OrionAerospace/SmashBoy/Estrutura e Acionamentos/Roda de reação/massa/dados roda de reaçao.pdf

Propriedades de massa de roda de reação
Configuração: Valor predeterminado
Sistema de coordenadas: -- valor predeterminado --

O centro da massa e os momentos de inércia são saídas no sistema de coordenadas de Montagem1 Densidade = 0.01 gramas por milímetro cúbico

Massa = 124.40 gramas

Volume = 15948.34 milímetros cúbicos

Área de superfície = 6283.67 milímetros quadrados

Centro de massa: ( milímetros )
X = -7.49
Y = -3.30
Z = 35.00

Eixos principais de inércia e momentos de inércia principais: ( gramas * milímetros quadrados ) Tomado no centro da massa.
Ix = ( 0.00, 0.00, 1.00) | Px = 23382.29
Iy = ( 1.00, 0.00, 0.00) | Py = 23382.29
Iz = ( 0.00, 1.00, 0.00) | Pz = 42605.02

Momentos de inércia: ( gramas * milímetros quadrados )
Obtido no centro de massa e alinhado com o sistema de coordenadas de saída.
Lxx = 23382.29 | Lxy = 0.00Lxz = 0.00
Lyx = 0.00 Lyy = 42605.02 | Lyz = 0.00
Lzx = 0.00Lzy = 0.00Lzz = 23382.29

Momentos de inércia: ( gramas * milímetros quadrados ) Tomados no sistema de coordenadas de saída.
Ixx = 177121.63 | Ixy = 3074.03 | Ixz = -32624.22
Iyx = 3074.03 | Iyy = 201975.89 | Iyz = -14358.64
Izx = -32624.22 | Izy = -14358.64 | Izz = 31719.72
