OrionAerospace/SmashBoy/ADCS/Orion_Sun_Sensor/SMASHBOY_AVI_ADC_PCB_PART02_V01.png

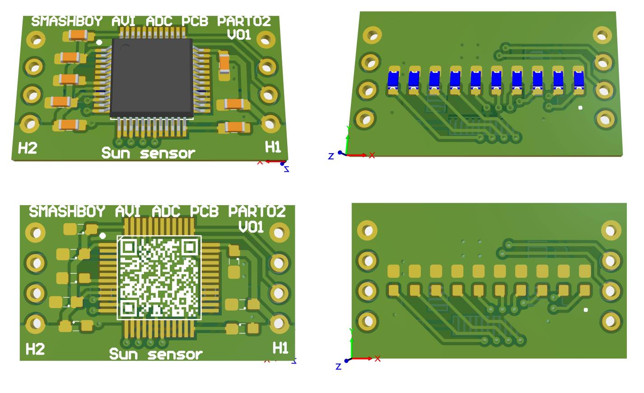
ADCS/Orion_Sun_Sensor/SMASHBOY_AVI_ADC_PCB_PART02_V01.png
