OrionAerospace/SmashBoy/Telemetria/Software/STM32/fluxograma RTOS V3.png

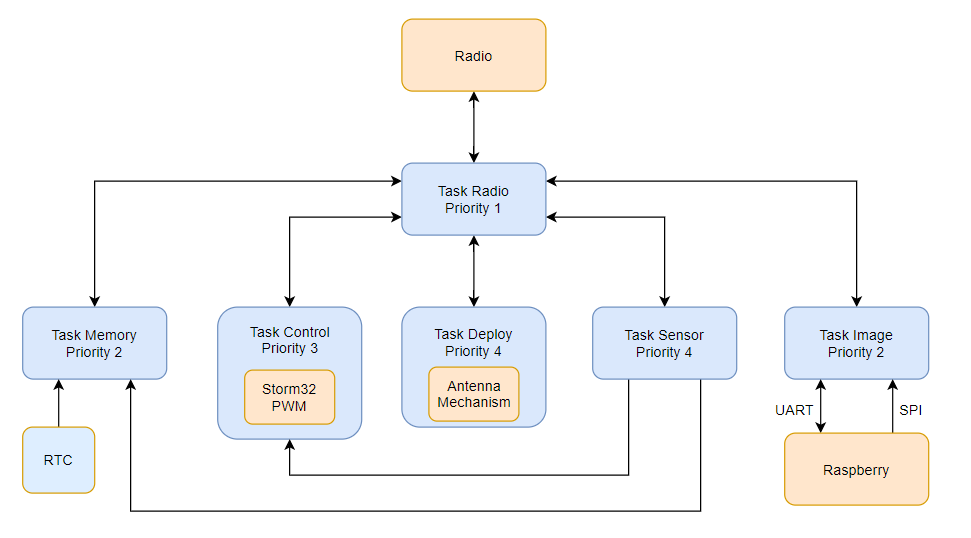
Telemetria/Software/STM32/fluxograma RTOS V3.png
