OrionAerospace/SmashBoy/Estrutura e Acionamentos/Roda de reação/massa/roda de reação.STEP

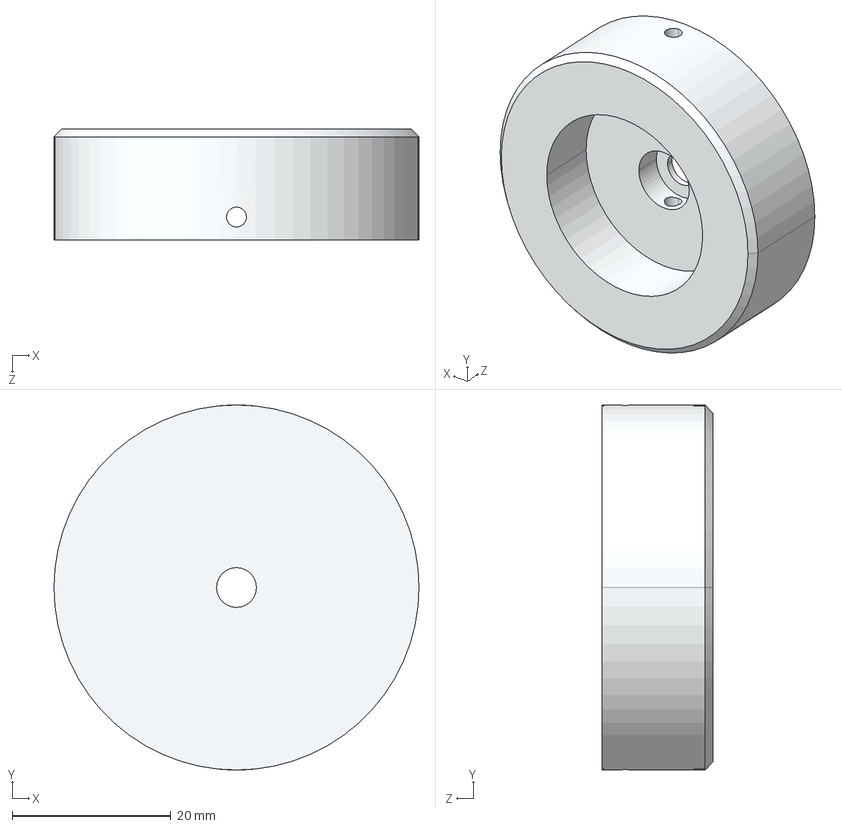
[picture p25: CAD file, 2021-03-11]
Estrutura e Acionamentos/Roda de reação/massa/roda de reação.STEP
46.0 x 46.0 x 14.0 mm
