OrionAerospace/SmashBoy/Estrutura e Acionamentos/Roda de reação/suporte.SLDPRT

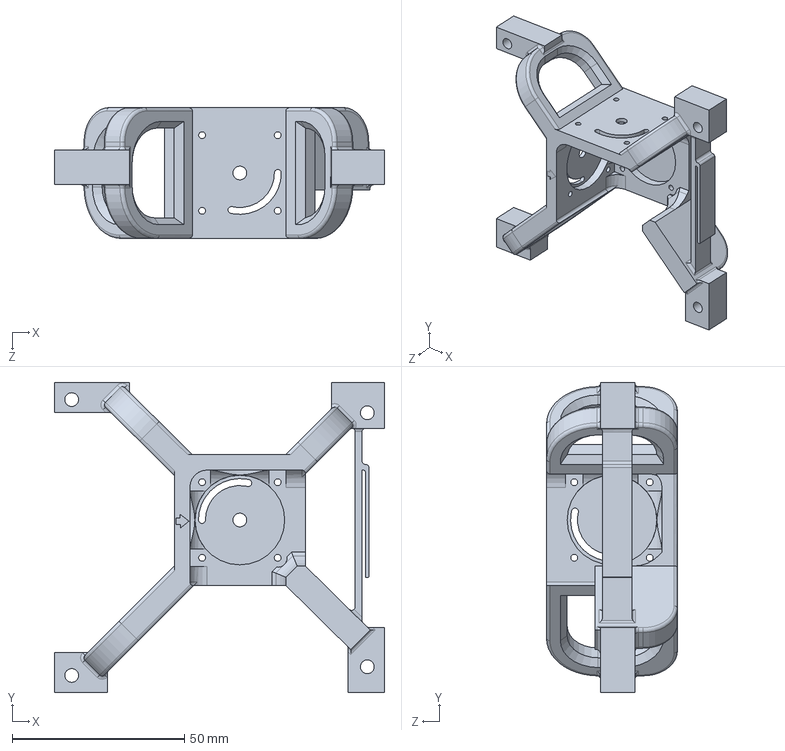
[picture p26: CAD file, 2021-02-28]
Estrutura e Acionamentos/Roda de reação/suporte.SLDPRT
95.7 x 90.0 x 38.0 mm
