OrionAerospace/SmashBoy/Estrutura e Acionamentos/trilhos/trilho-deploy-switch.SLDPRT

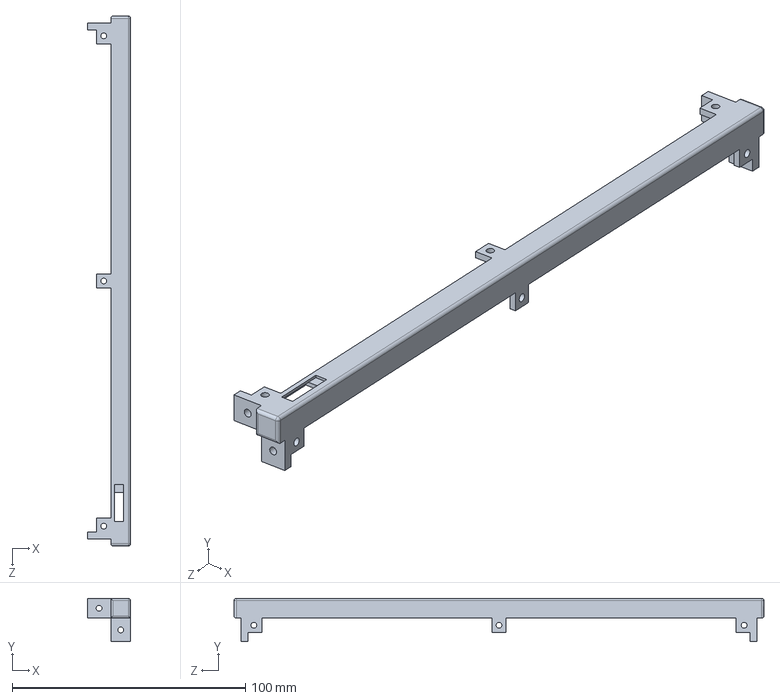
[picture p27: CAD file, 2020-08-22]
Estrutura e Acionamentos/trilhos/trilho-deploy-switch.SLDPRT
18.5 x 18.5 x 227.0 mm
