OrionAerospace/SmashBoy/ADCS/SETUP_ADCS/antigo/L3.SLDPRT

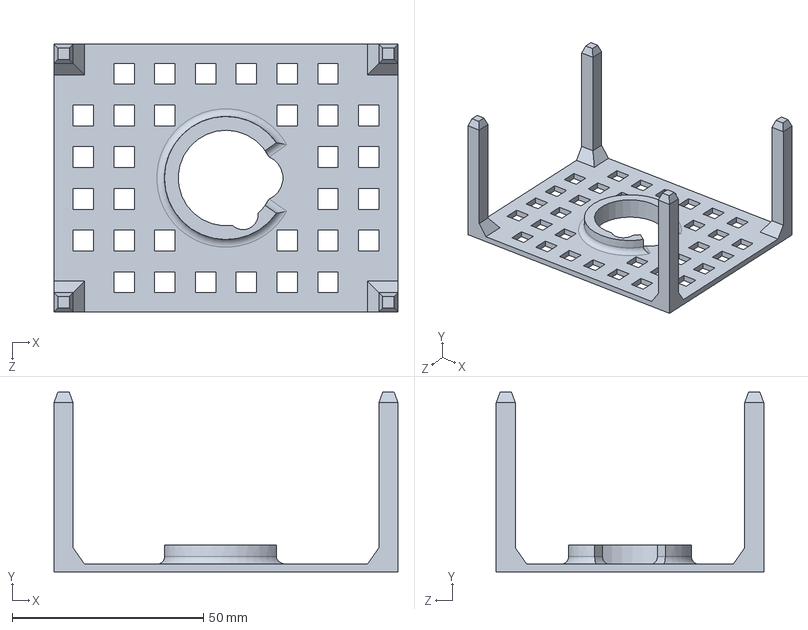
[picture p28: CAD file, 2021-07-17]
ADCS/SETUP_ADCS/antigo/L3.SLDPRT
90.0 x 47.0 x 70.0 mm
