OrionAerospace/SmashBoy/ADCS/SETUP_ADCS/STL/suporte_M.STL

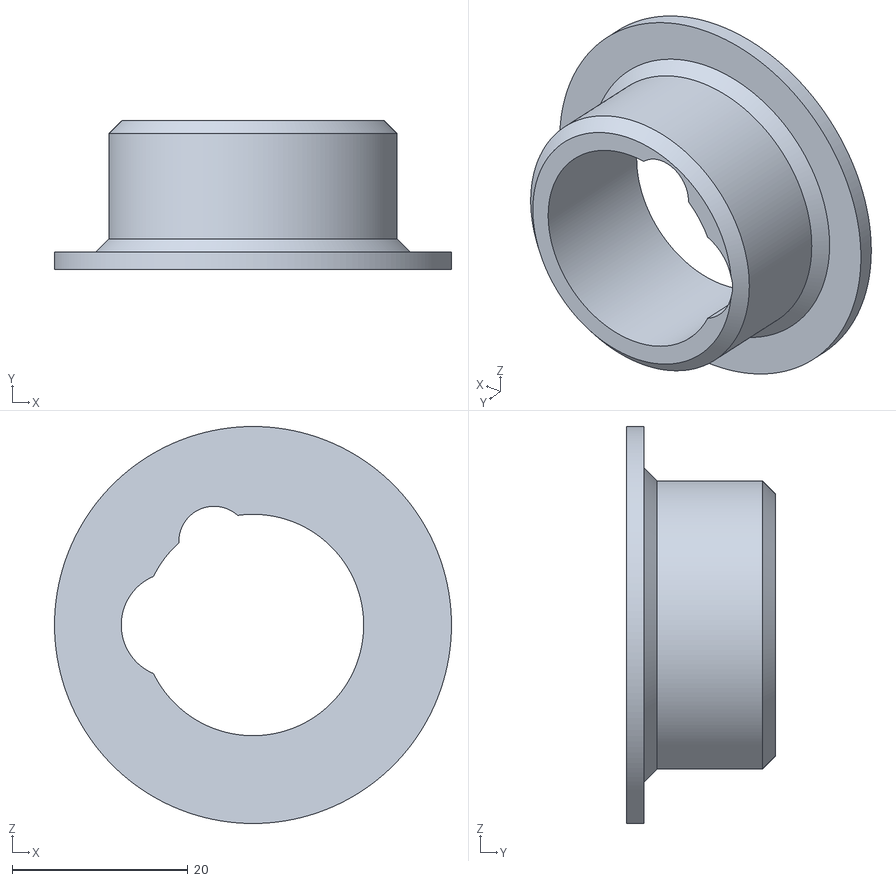
[picture p29: CAD file, 2021-07-17]
ADCS/SETUP_ADCS/STL/suporte_M.STL
45.2 x 17.0 x 45.2
