OrionAerospace/SmashBoy/ADCS/SETUP_ADCS/antigo/L2_A.SLDPRT

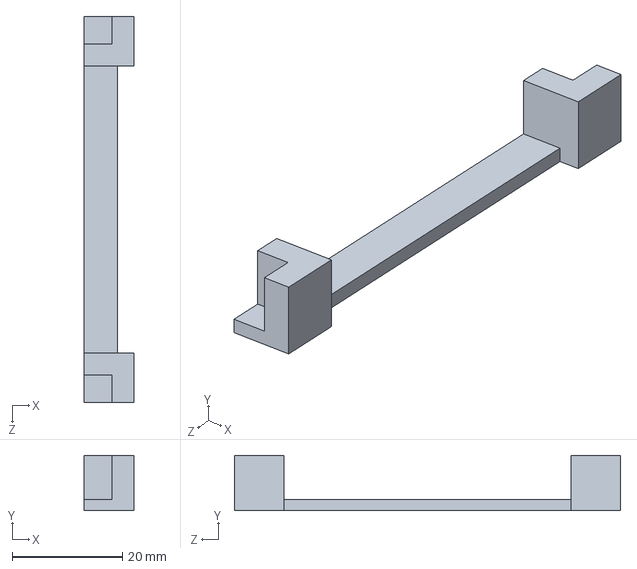
[picture p30: CAD file, 2021-07-17]
ADCS/SETUP_ADCS/antigo/L2_A.SLDPRT
9.00 x 10.0 x 70.0 mm
