OrionAerospace/SmashBoy/ADCS/SETUP_ADCS/STL/L2_A_v2.STL

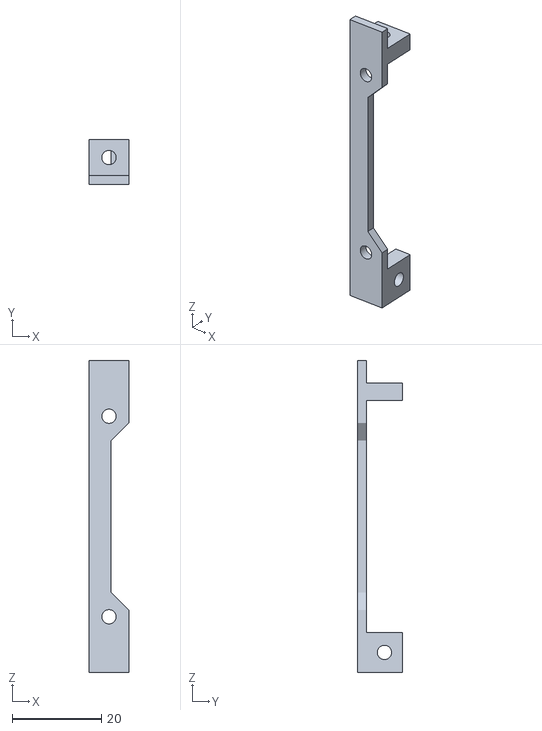
[picture p31: CAD file, 2021-07-17]
ADCS/SETUP_ADCS/STL/L2_A_v2.STL
9.00 x 10.0 x 70.0
