OrionAerospace/SmashBoy/ADCS/SETUP_ADCS/STL/L3_v2.STL

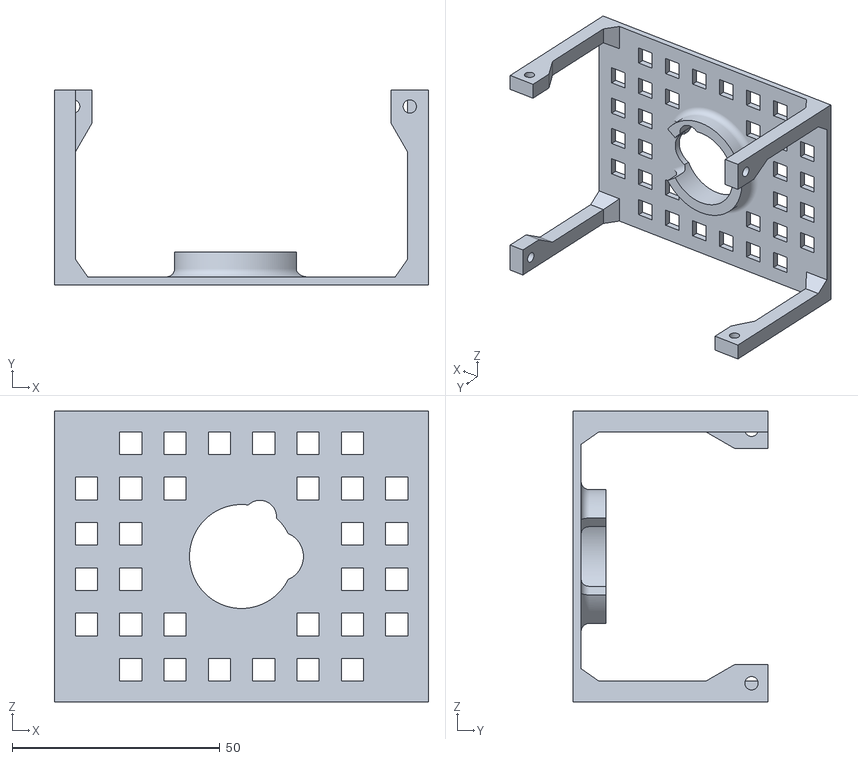
[picture p32: CAD file, 2021-07-17]
ADCS/SETUP_ADCS/STL/L3_v2.STL
90.0 x 47.0 x 70.0
