OrionAerospace/SmashBoy/Estrutura e Acionamentos/peça esqueleto/peça esqueleto-v2.PDF

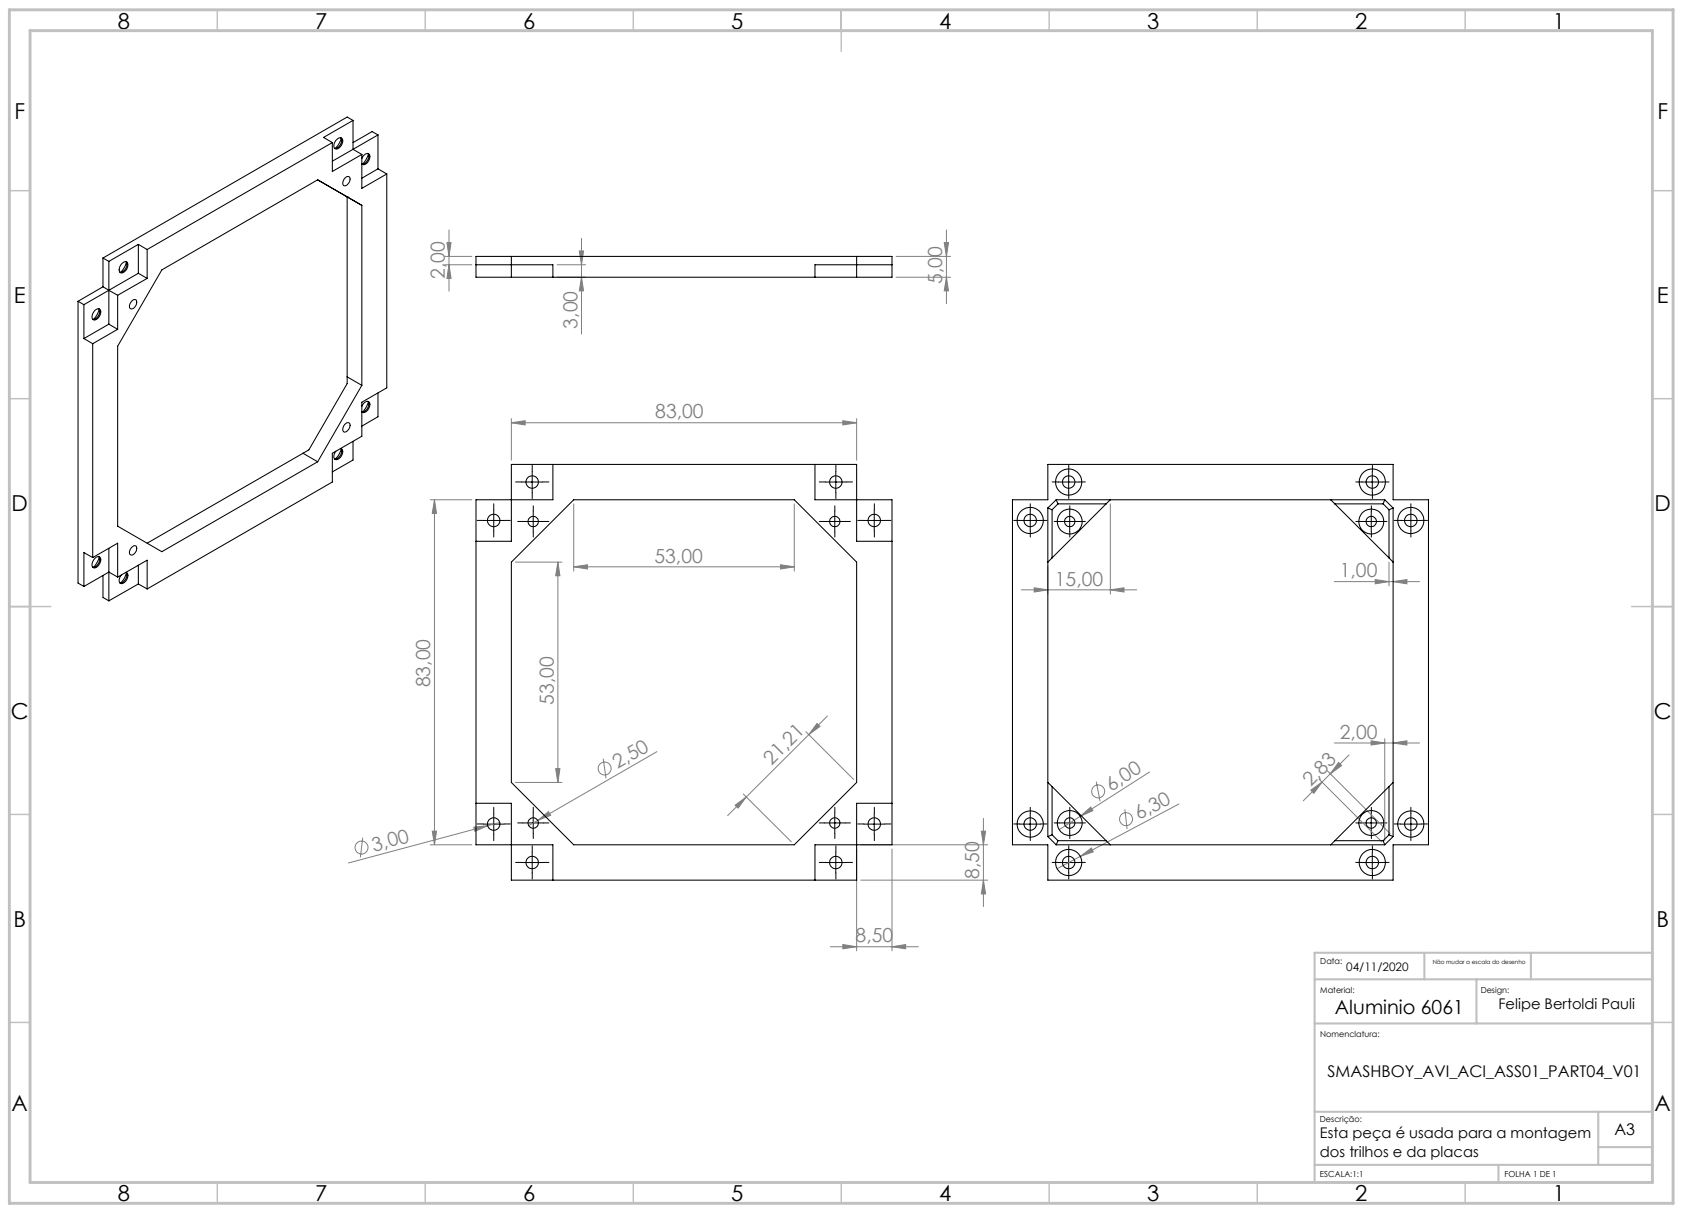
[picture p44: page 1]
ESCALA:1:1; FOLHA 1 DE 1

Data: 04/11/2020 | Não mudar a escala do desenho

Material: Aluminio 6061 | Design: Felipe Bertoldi Pauli

Descrição:
Esta peça é usada para a montagem
dos trilhos e da placas
