OrionAerospace/SmashBoy/Estrutura e Acionamentos/Fixação das placas/fixação placas -face -z.PDF

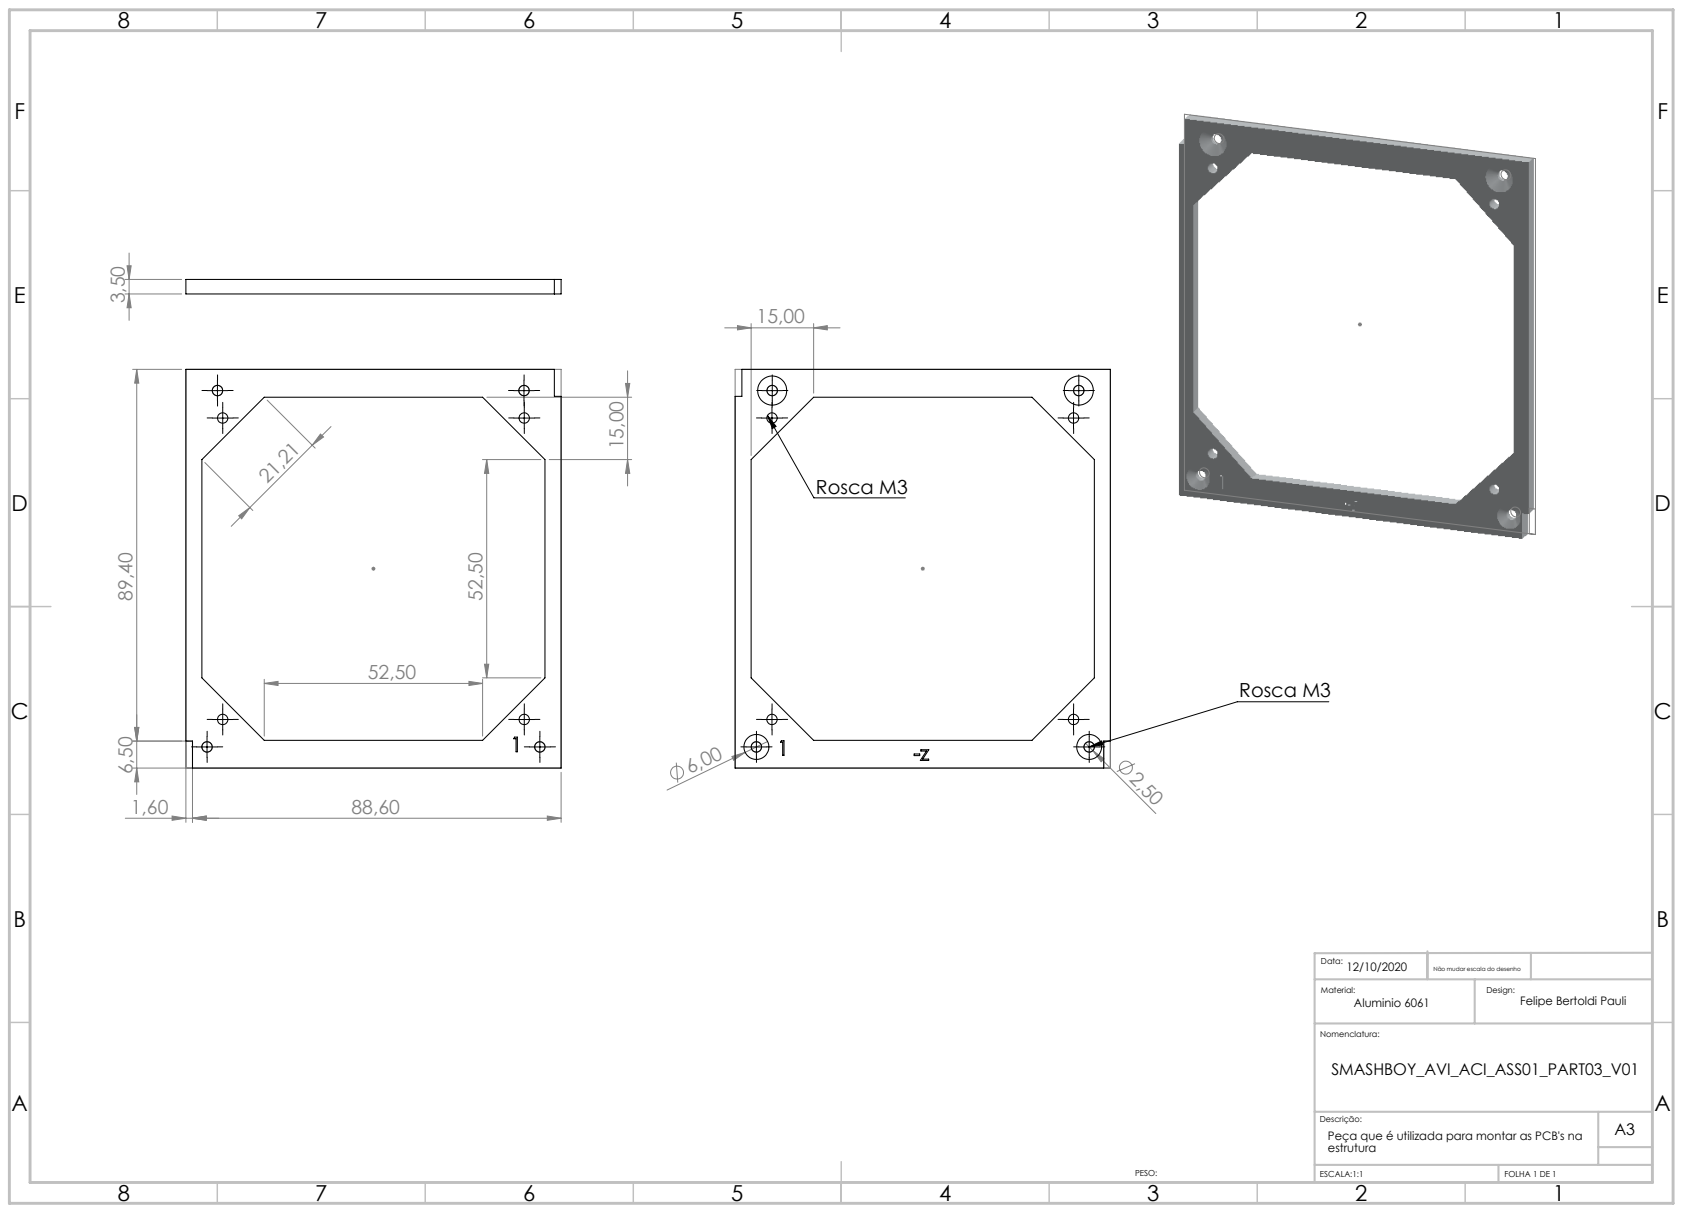
[picture p45: page 1]
Rosca M3; ESCALA:1:1; FOLHA 1 DE 1

Data: 12/10/2020 | Não mudar escala do desenho

Material: Aluminio 6061 | Design: Felipe Bertoldi Pauli

Descrição:
Peça que é utilizada para montar as PCB's na
estrutura
