OrionAerospace/SmashBoy/Energia/SMASHBOY_AVI_ENE_PCB_PART02_V01/PDF/SMASHBOY_AVI_ENE_PCB_PART02_V01.pdf

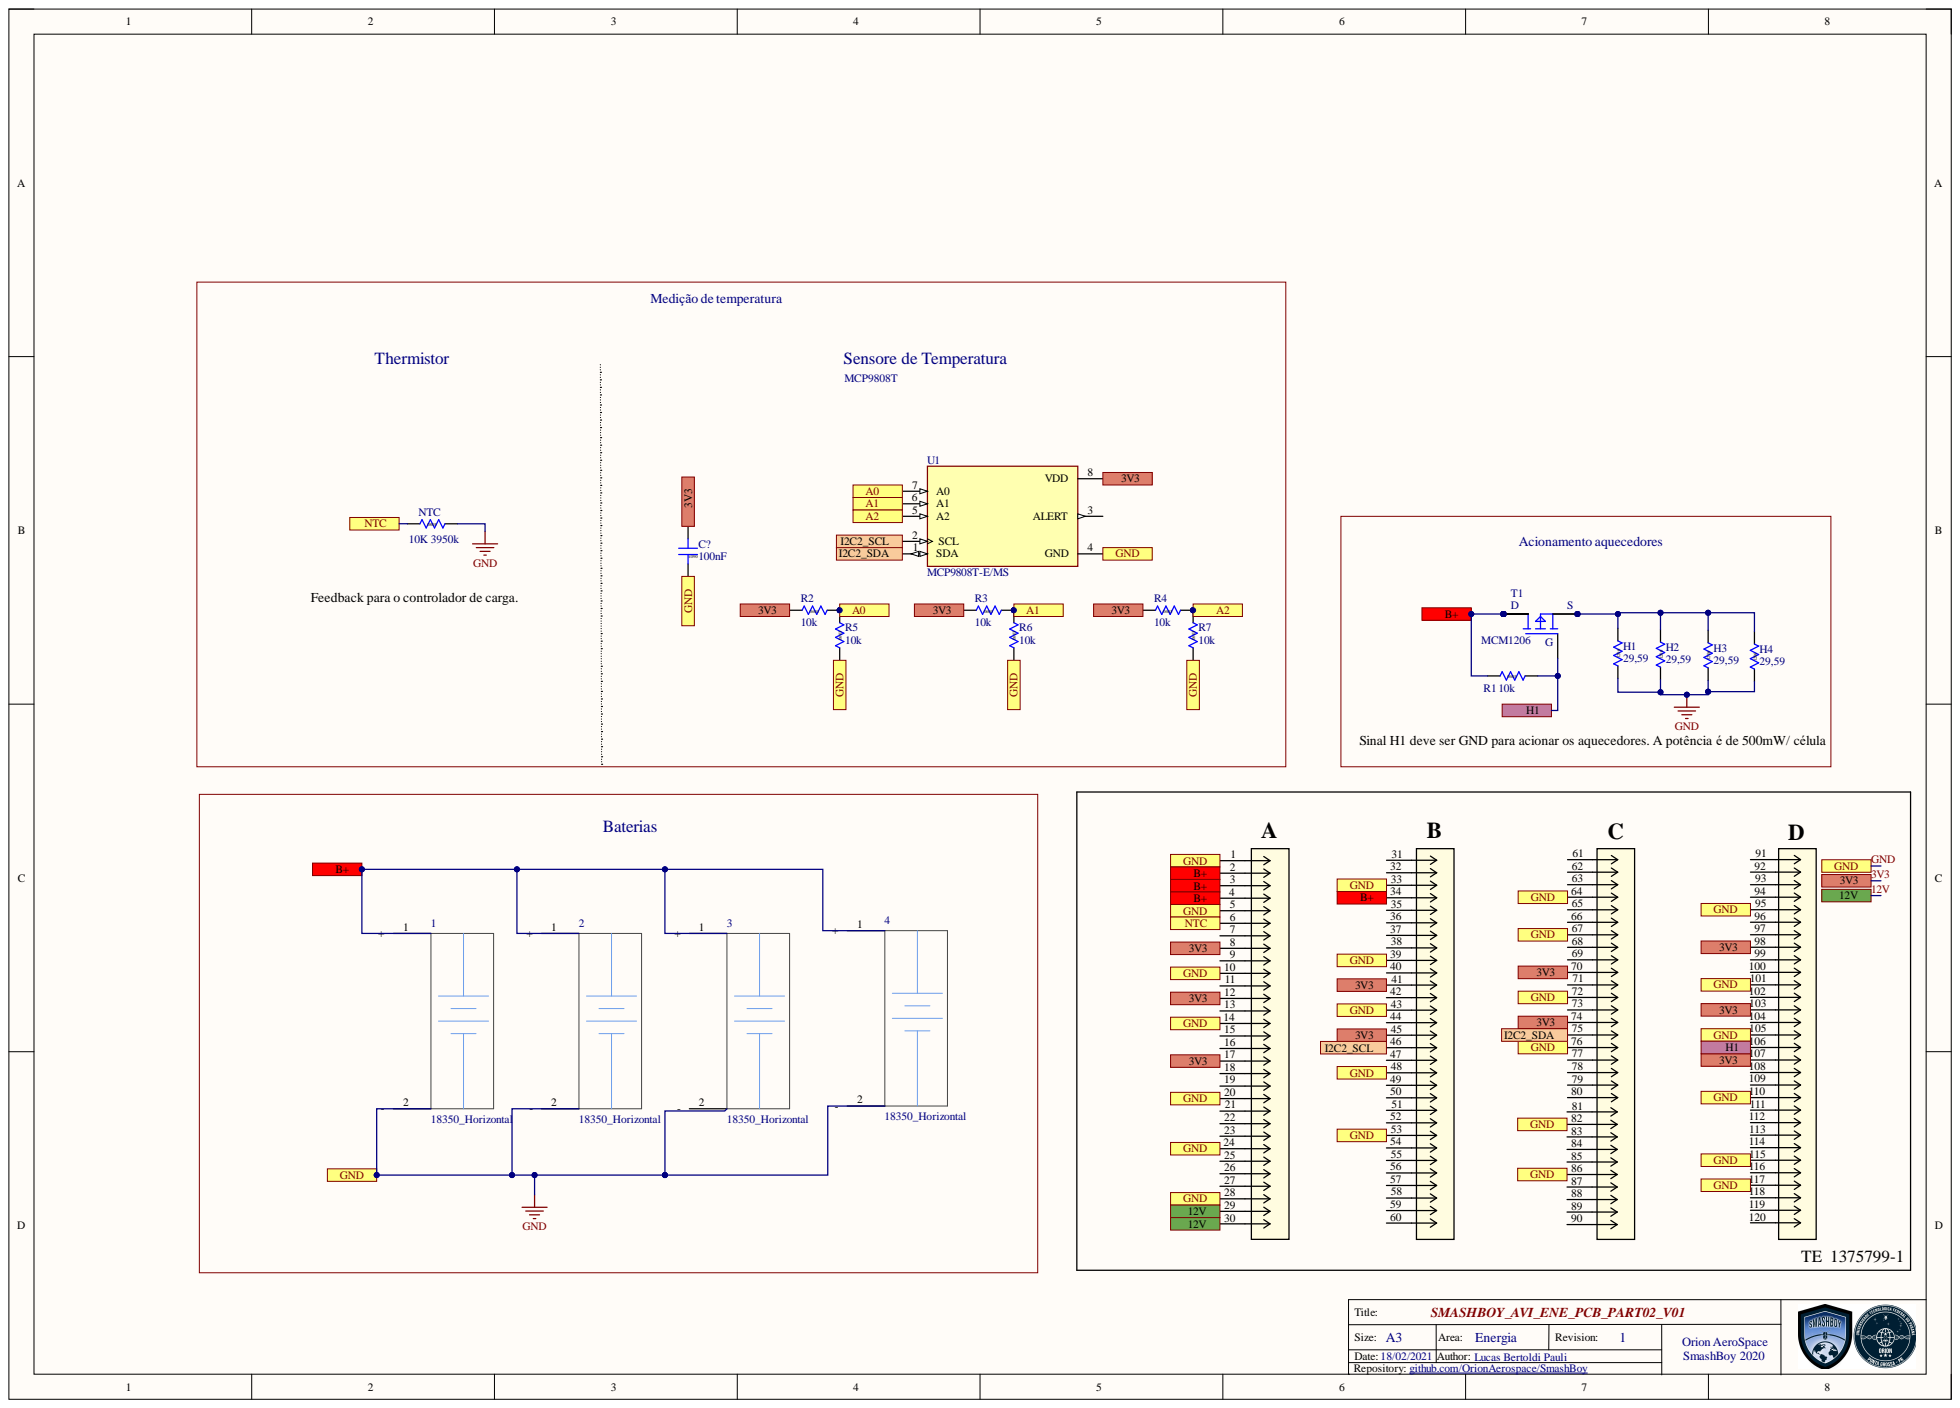
[picture p46: page 1]

A0 | A1 6
A1 | A2 5

I2C2_SCL | SDA 1
I2C2_SDA | | GND

Feedback para o controlador de carga.

Sinal H1 deve ser GND para acionar os aquecedores. A potência é de 500mW/ célula

Size: | Area: Energia | 1
Date: 18/02/2021
