OrionAerospace/SmashBoy/Energia/SMASHBOY_AVI_ENE_PCB_PART01_V01/PDF/SMASHBOY_AVI_ENE_PCB_PART01_V01.pdf

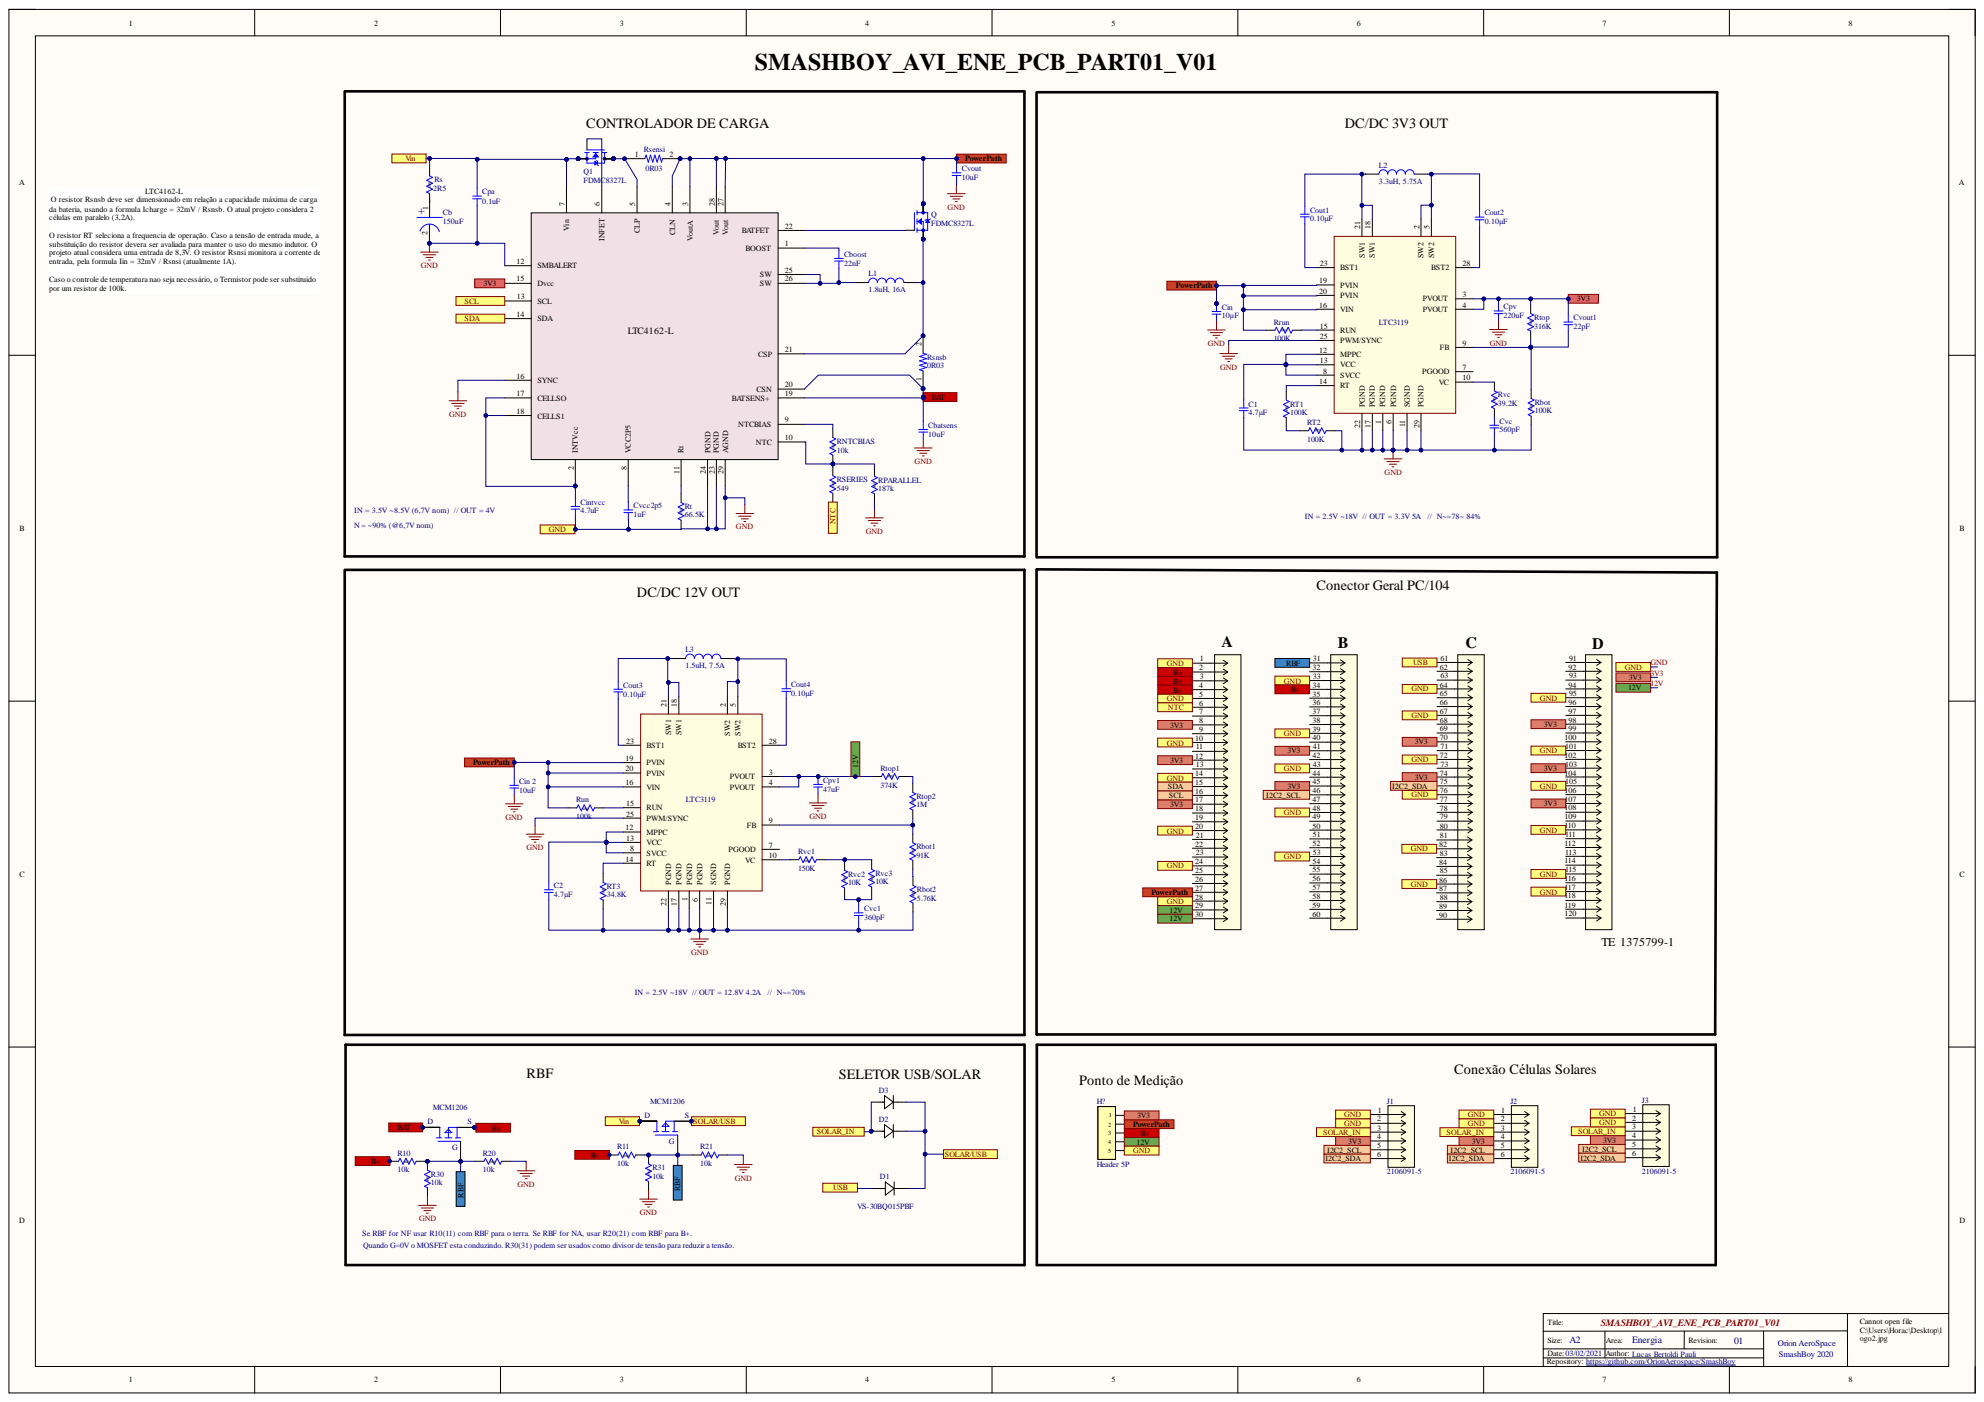
[picture p47: page 1]

O resistor Rsnsb deve ser dimensionado em relação a capacidade máxima de carga
da bateria, usando a formula Icharge = 32mV / Rsnsb. O atual projeto considera 2
células em paralelo (3,2A).

O resistor RT seleciona a frequencia de operação. Caso a tensão de entrada mude, a
substituição do resistor devera ser avaliada para manter o uso do mesmo indutor. O
projeto atual considera uma entrada de 8,3V. O resistor Rsnsi monitora a corrente de
entrada, pela formula Iin = 32mV / Rsnsi (atualmente 1A).

Caso o controle de temperatura nao seja necessário, o Termistor pode ser substituido
por um resistor de 100k.

VCC 13
SVCC 8

IN = 2.5V ~18V // OUT = 3.3V 5A // N~=78~ 84% IN = 3.5V ~8.5V (6,7V nom) // OUT = 4V

Se RBF for NF usar R10(11) com RBF para o terra. Se RBF for NA, usar R20(21) com RBF para B+.
Quando G=0V o MOSFET esta conduzindo. R30(31) podem ser usados como divisor de tensão para reduzir a tensão.

Size: | Area: Energia | 01

Date: 03/02/2021
