OrionAerospace/SmashBoy/Estrutura e Acionamentos/Roda de reação/massa/roda de reação_AL_V2.PDF

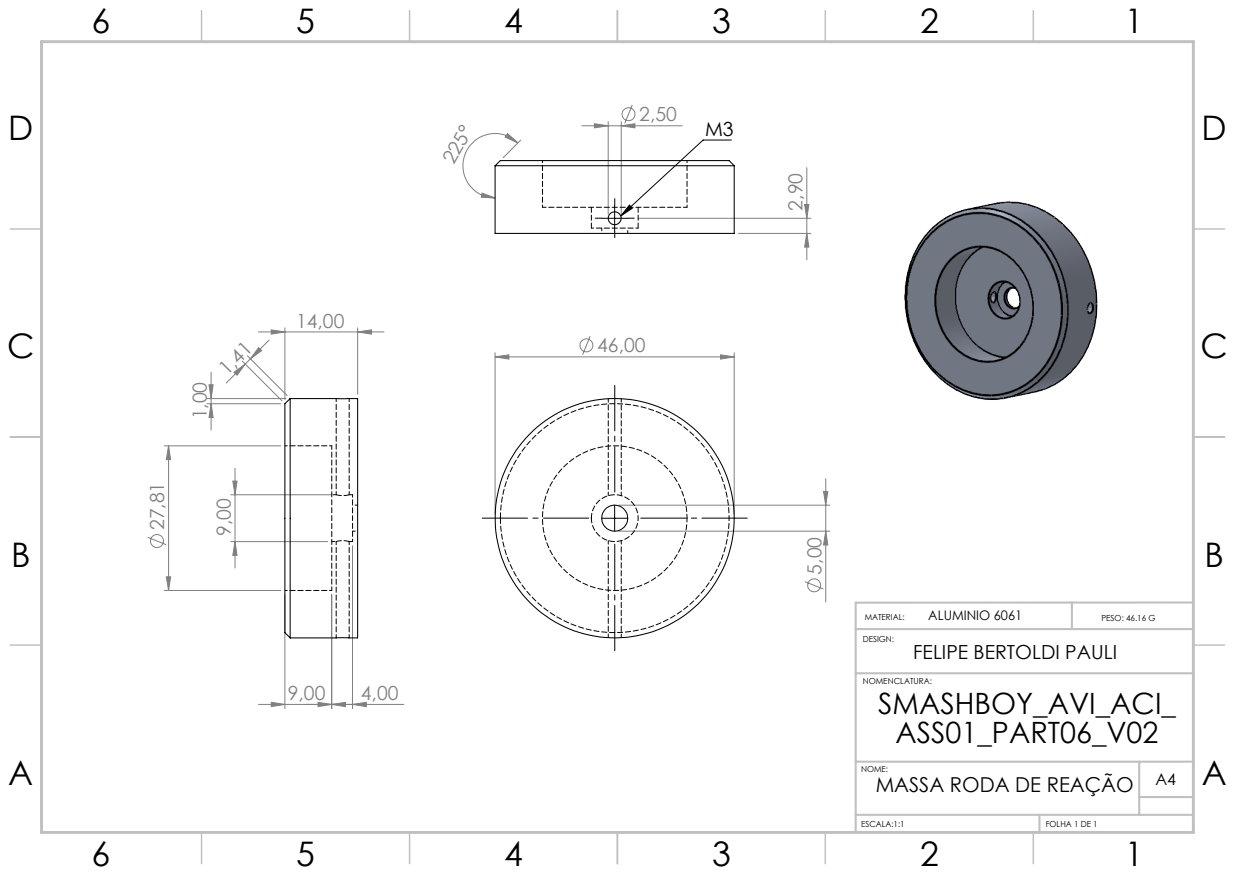
[picture p51: page 1]
ESCALA:1:1; FOLHA 1 DE 1; ALUMINIO 6061; PESO: 46.16 G; FELIPE BERTOLDI PAULI

NOME:
MASSA RODA DE REAÇÃO
