OrionAerospace/SmashBoy/Estrutura e Acionamentos/Roda de reação/massa/roda de reação_nylon.PDF

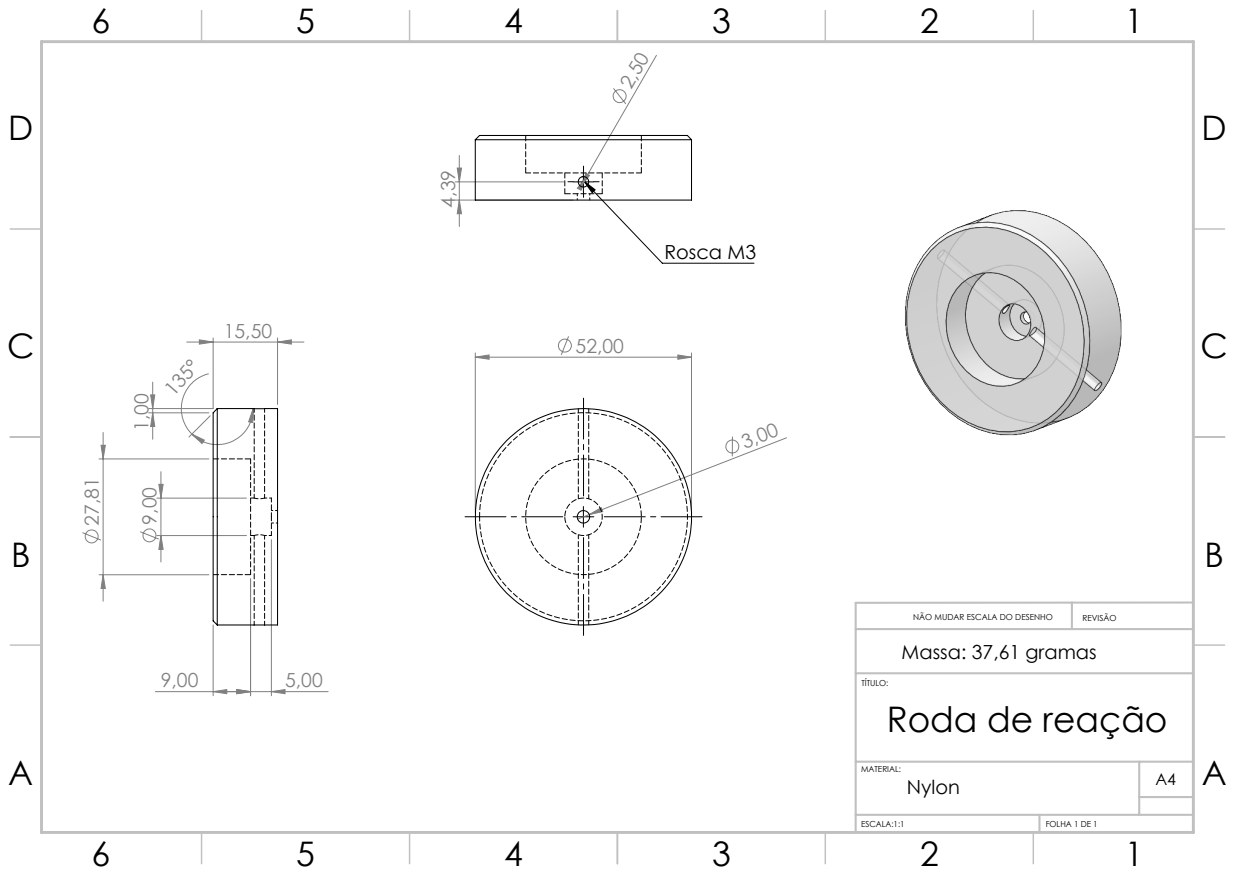
[picture p52: page 1]
Rosca M3; NÃO MUDAR ESCALA DO DESENHO; REVISÃO; ESCALA:1:1; FOLHA 1 DE 1

Massa: 37,61 gramas
Roda de reação
