OrionAerospace/SmashBoy/Estrutura e Acionamentos/Roda de reação/massa/roda de reação-Desenho.PDF

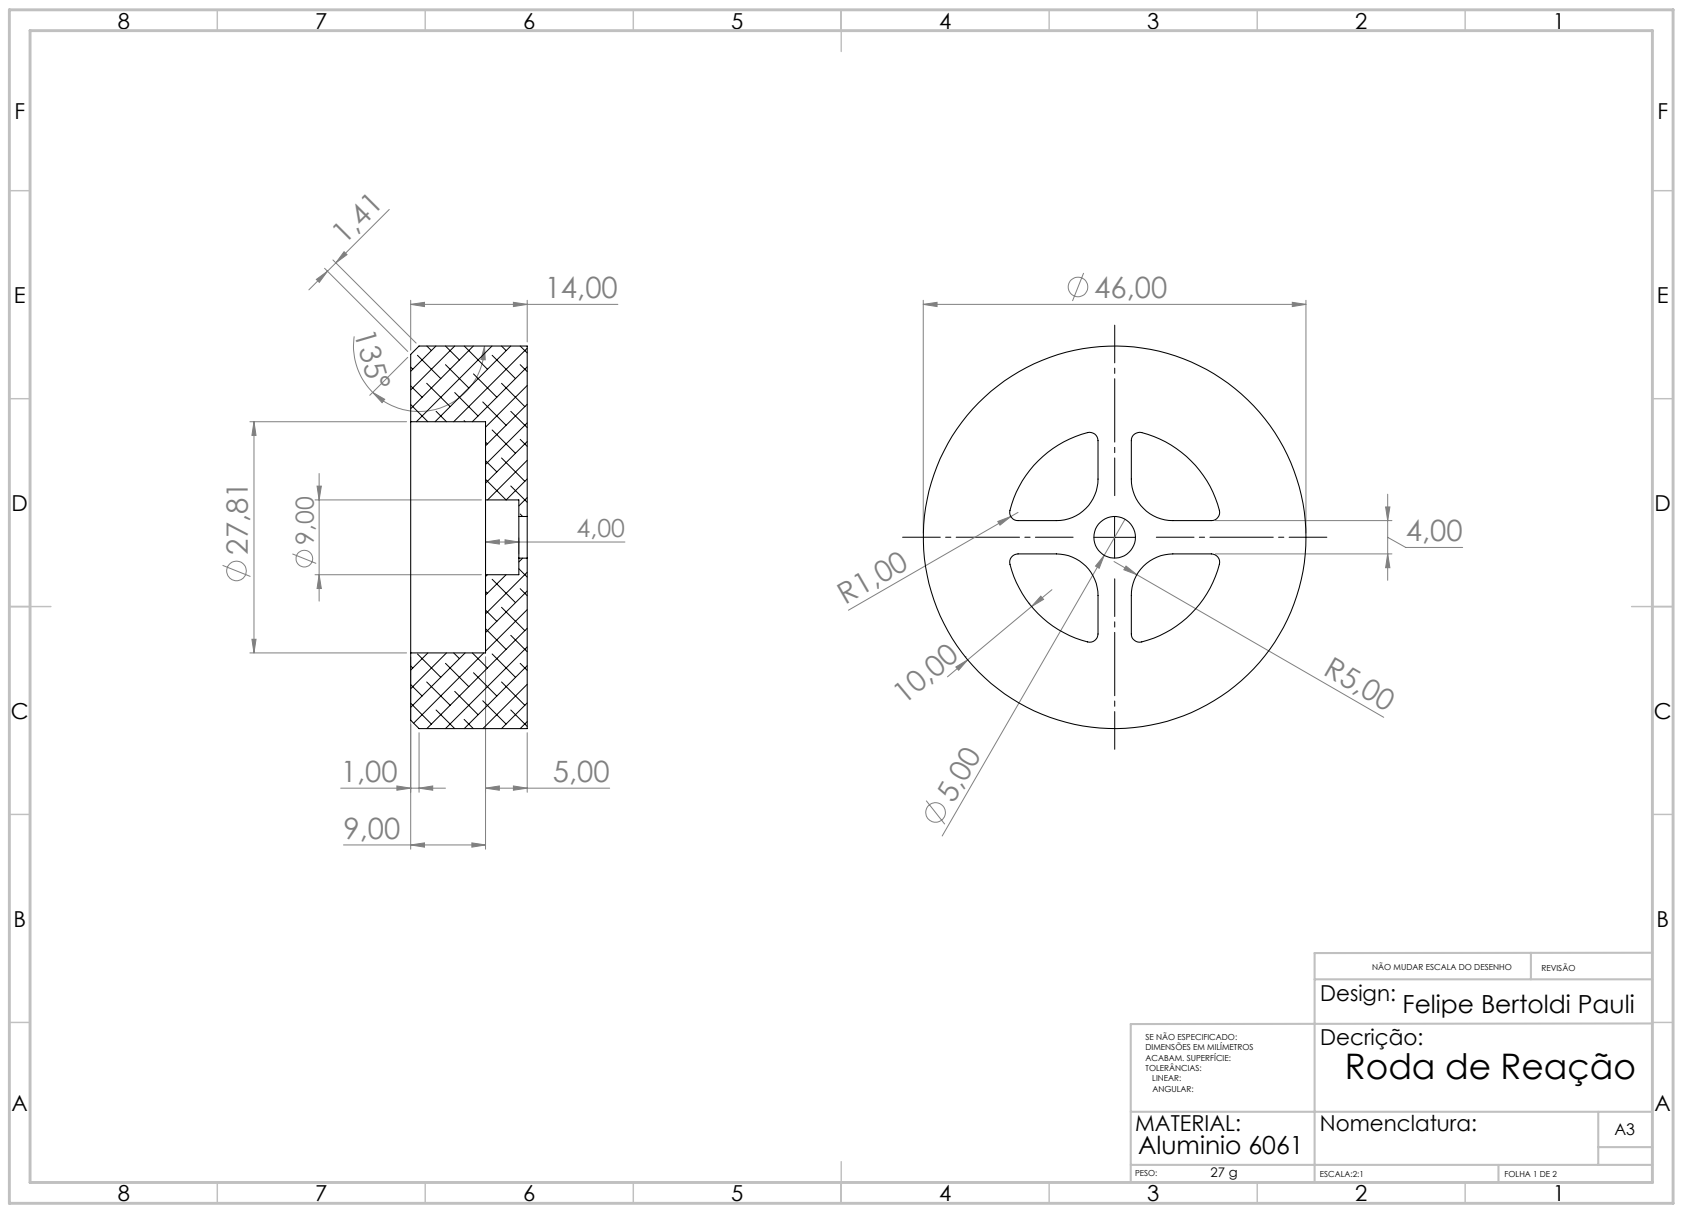
[picture p53: page 1]
NÃO MUDAR ESCALA DO DESENHO; REVISÃO; ESCALA:2:1; FOLHA 1 DE 2

Felipe Bertoldi Pauli Design:

SE NÃO ESPECIFICADO: DIMENSÕES EM MILÍMETROS ACABAM. SUPERFÍCIE: TOLERÂNCIAS: LINEAR: ANGULAR: | Decrição: Roda de Reação

MATERIAL: Aluminio 6061 | Nomenclatura: | A3

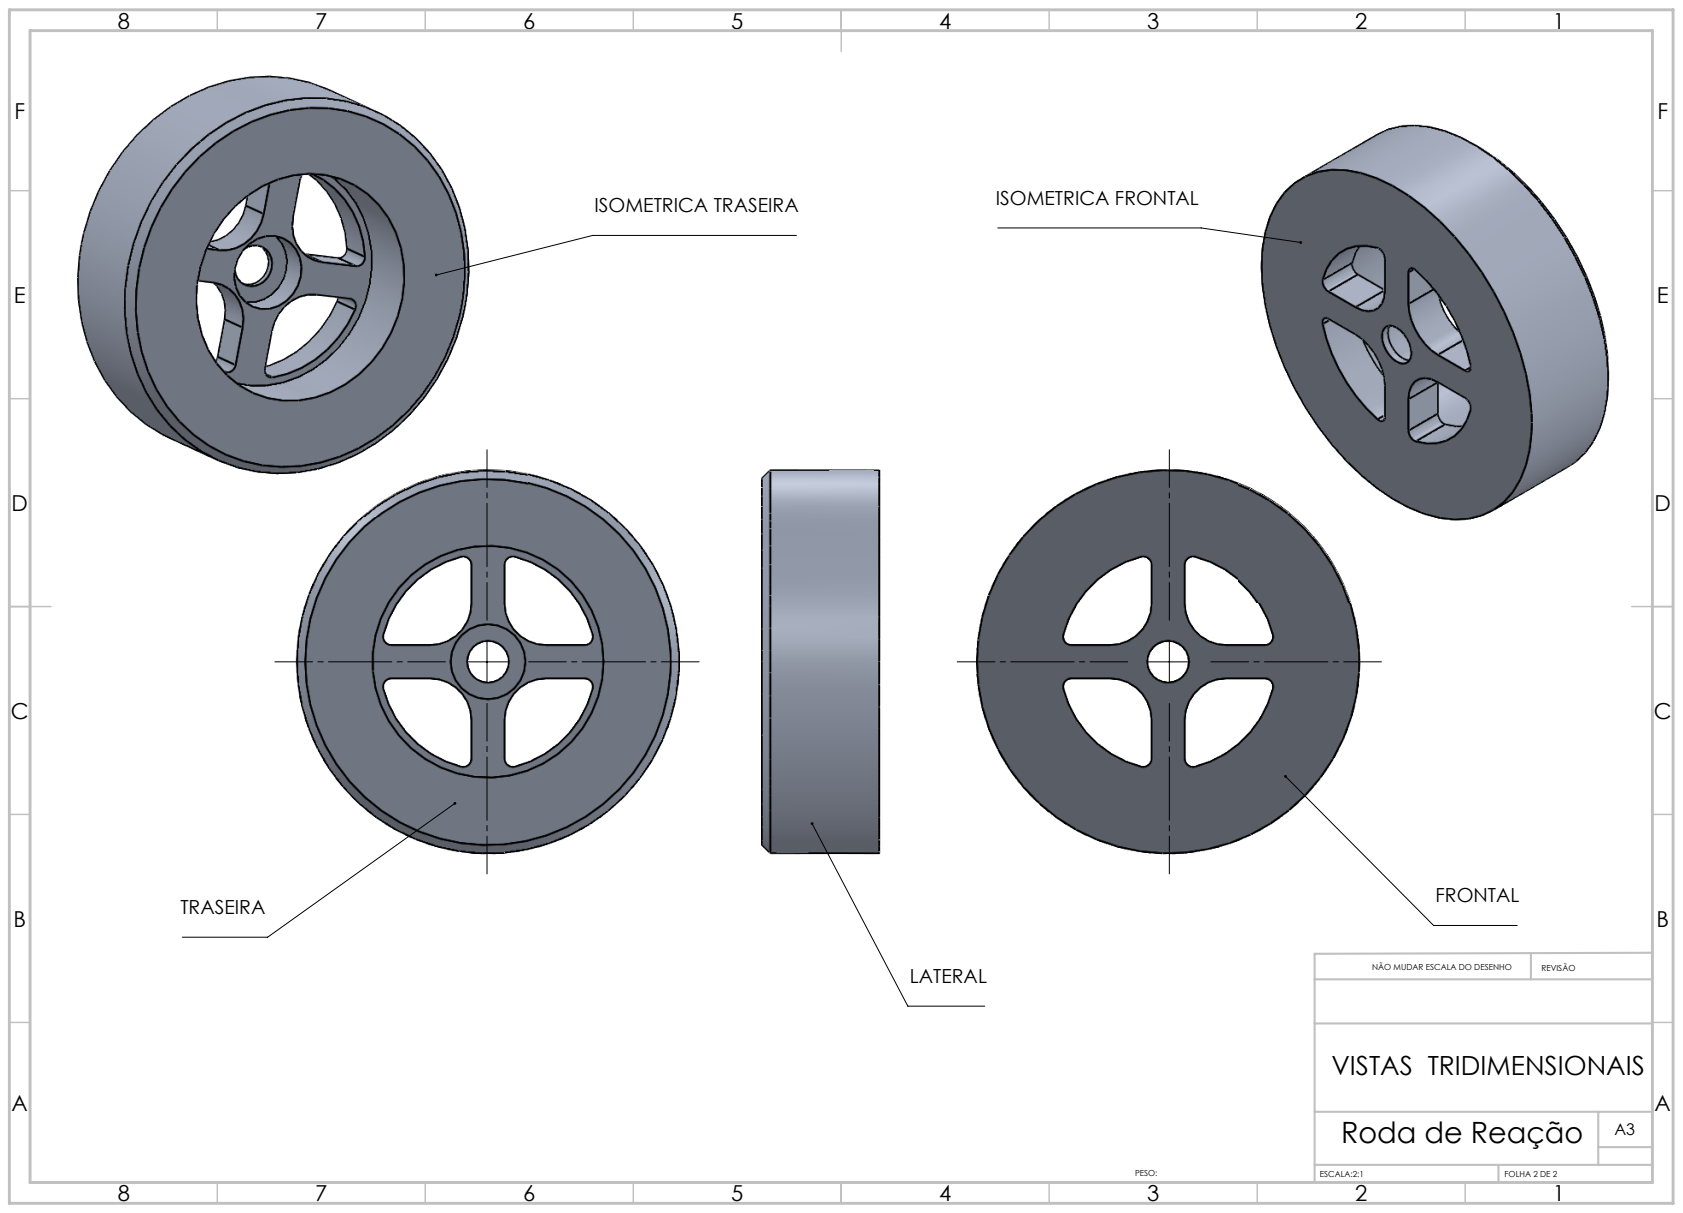
[picture p54: page 2]
NÃO MUDAR ESCALA DO DESENHO; REVISÃO; ESCALA:2:1; FOLHA 2 DE 2

ISOMETRICA FRONTAL ISOMETRICA TRASEIRA

VISTAS TRIDIMENSIONAIS
Roda de Reação
