OrionAerospace/SmashBoy/Energia/SMASHBOY_AVI_ENE_PCB_PART03_V01/PDF/SMASHBOY_AVI_ENE_PCB_PART03_V01.pdf

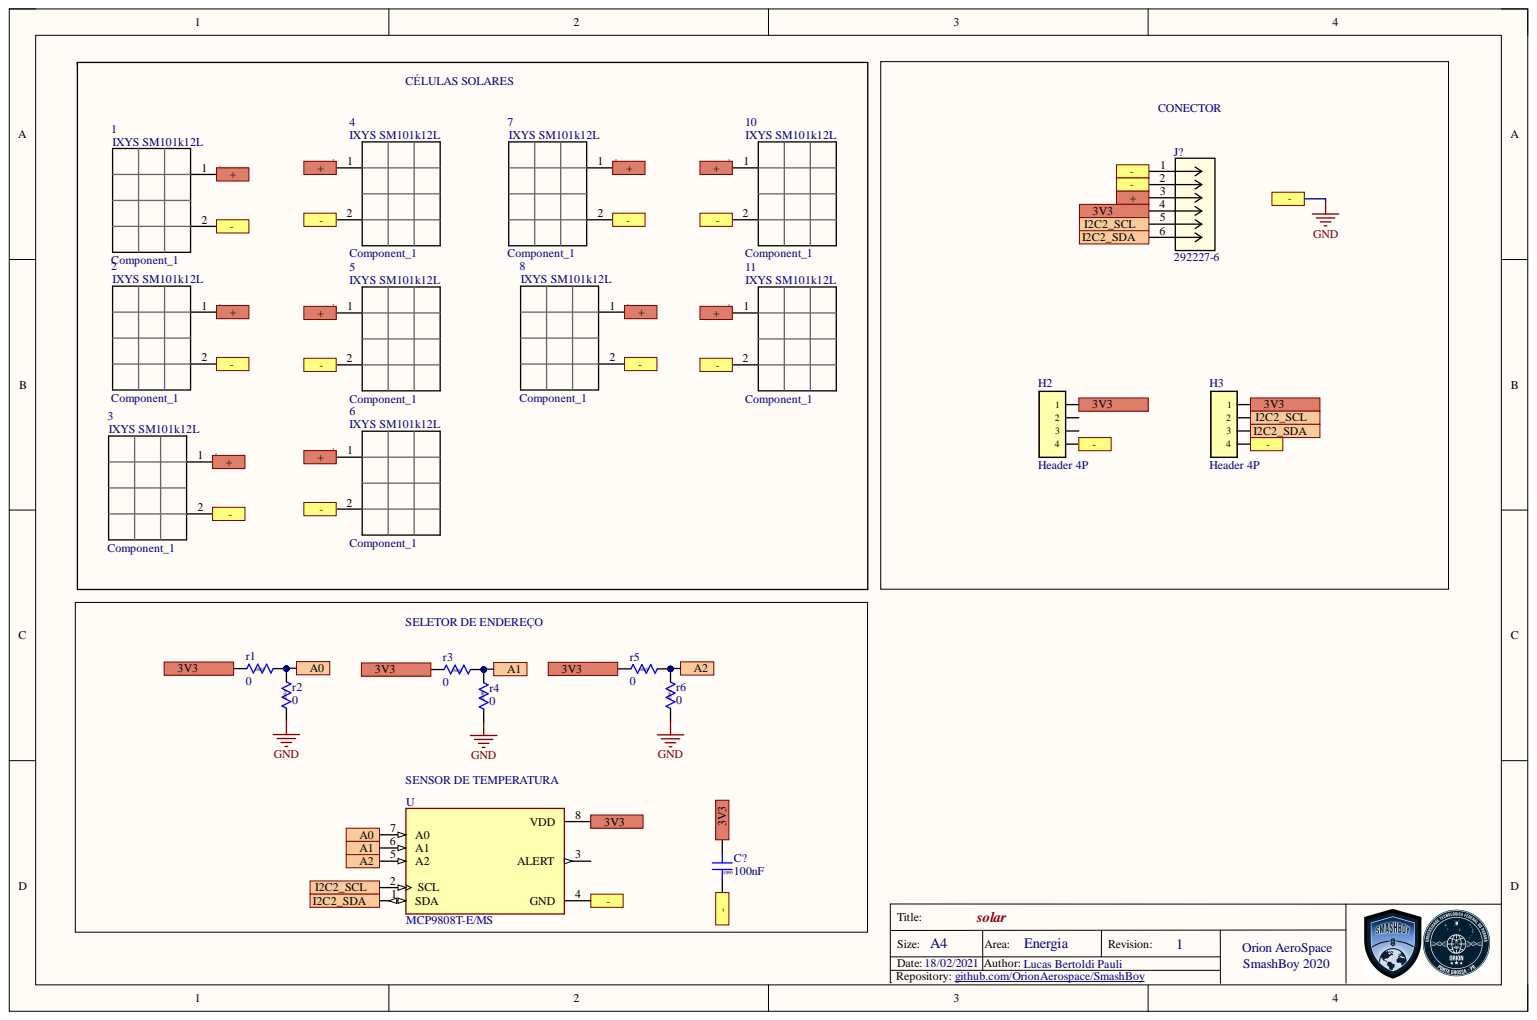
[picture p55: page 1]

Size: | Area: Energia | 1

Date: 18/02/2021

Repository: github.com/OrionAerospace/SmashBoy
